kevinaangstadt/ARC86-512/hardware/ARC86-512.kicad_sch

## KiCad design hardware/ARC86-512.kicad_sch (2025-04-01, an earlier design)

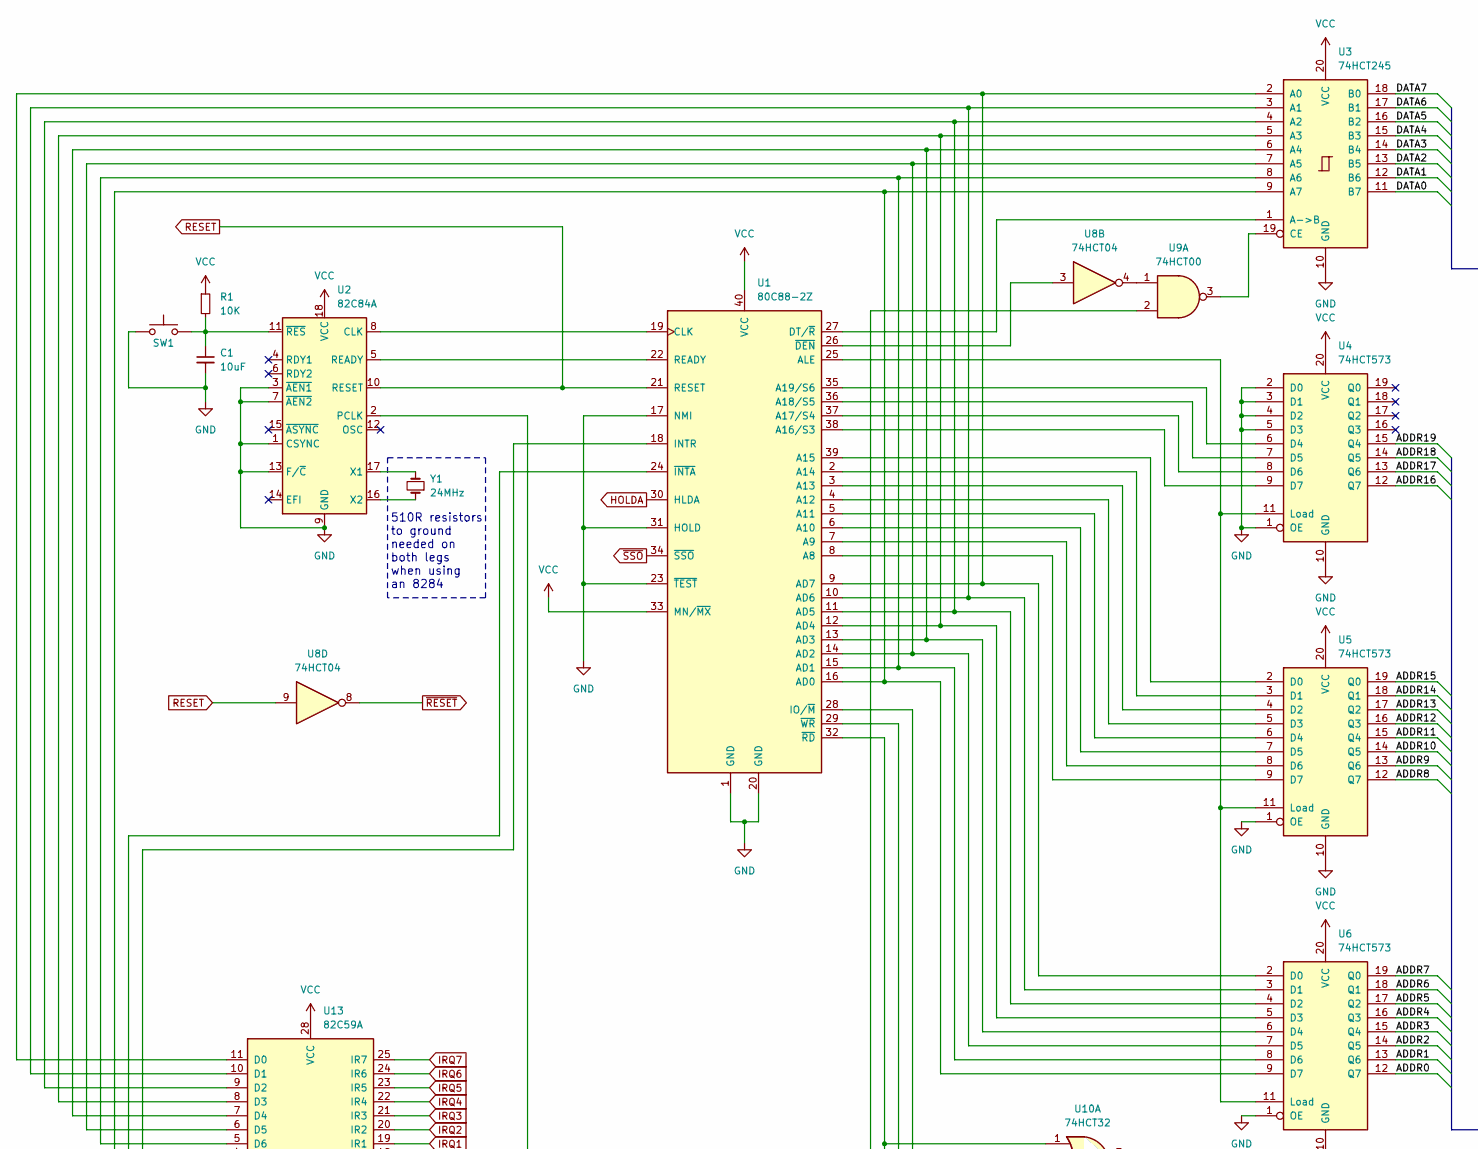
[picture p5: schematic ARC86-512.kicad_sch, part in row 1, column 1]

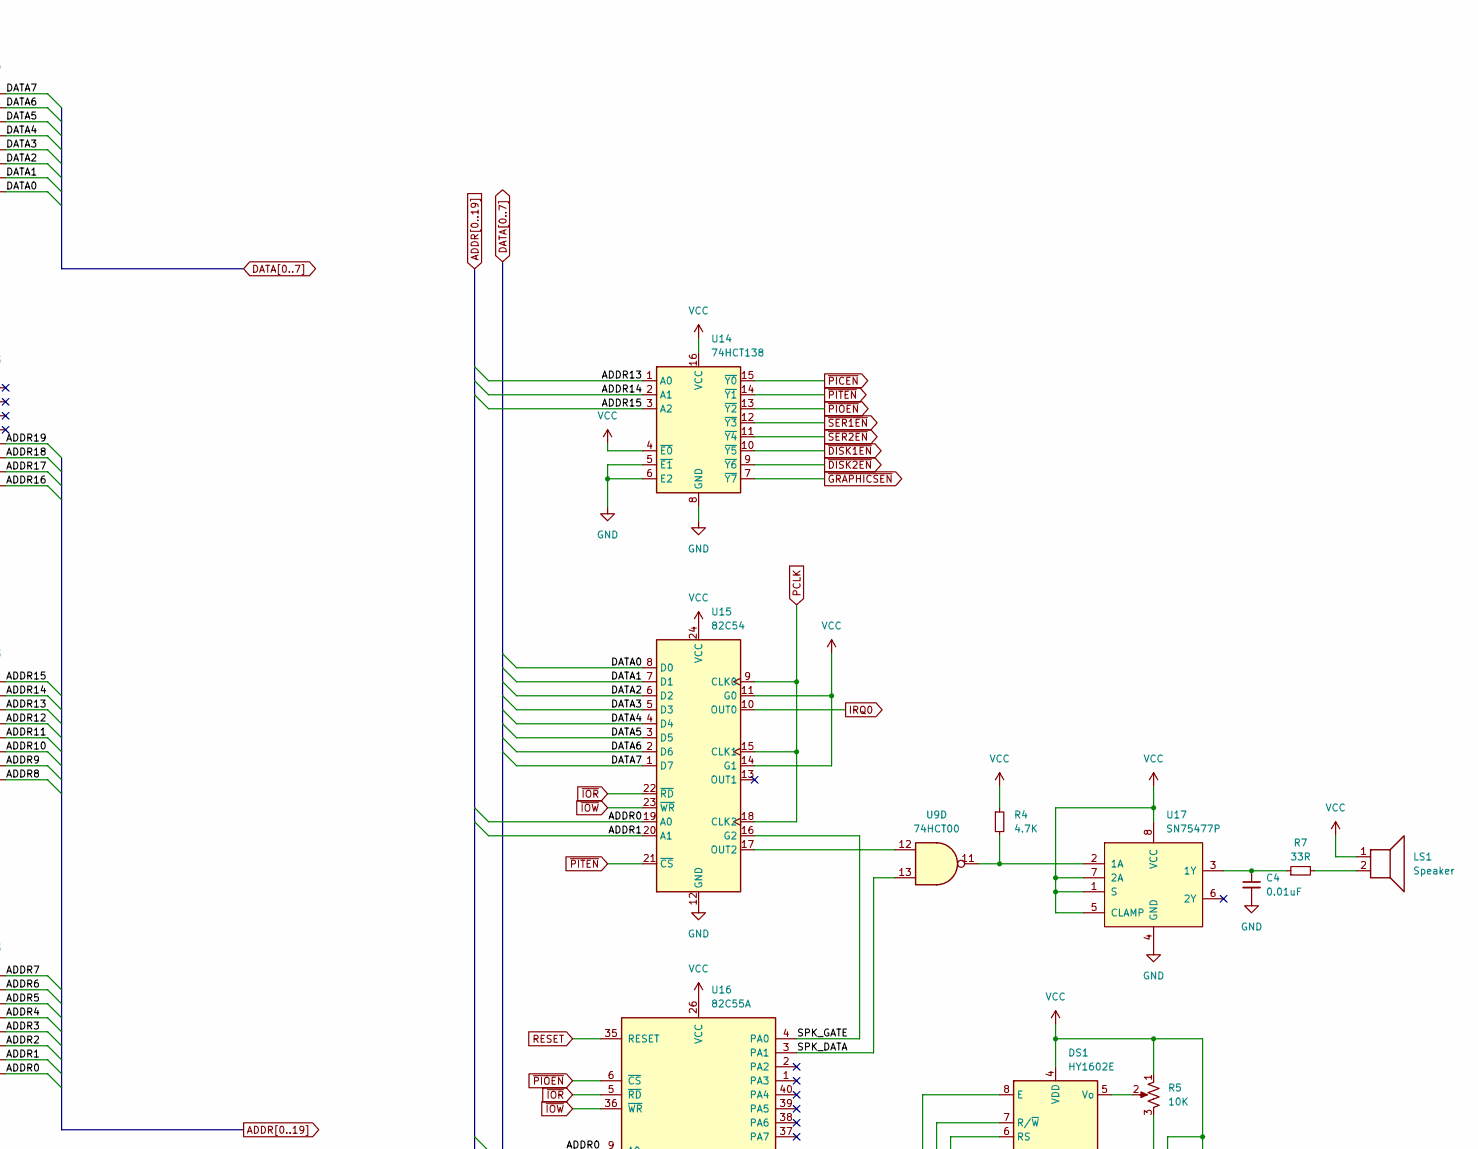
[picture p6: schematic ARC86-512.kicad_sch, part in row 1, column 2]

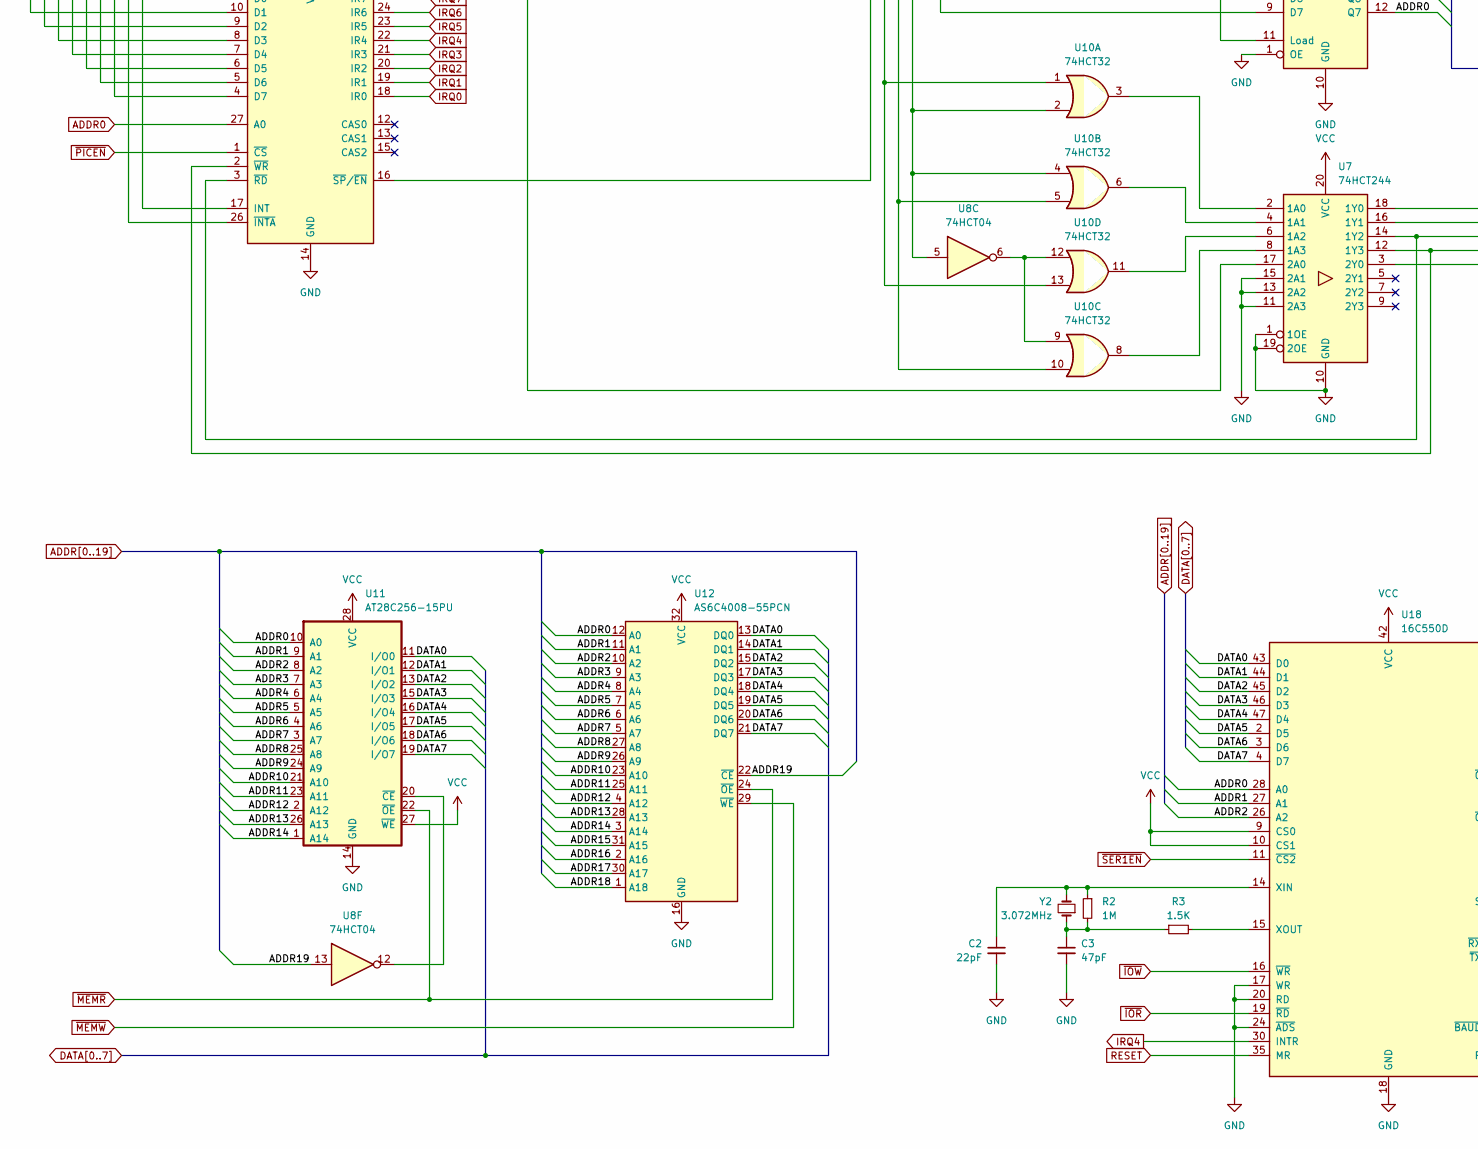
[picture p7: schematic ARC86-512.kicad_sch, part in row 2, column 1]

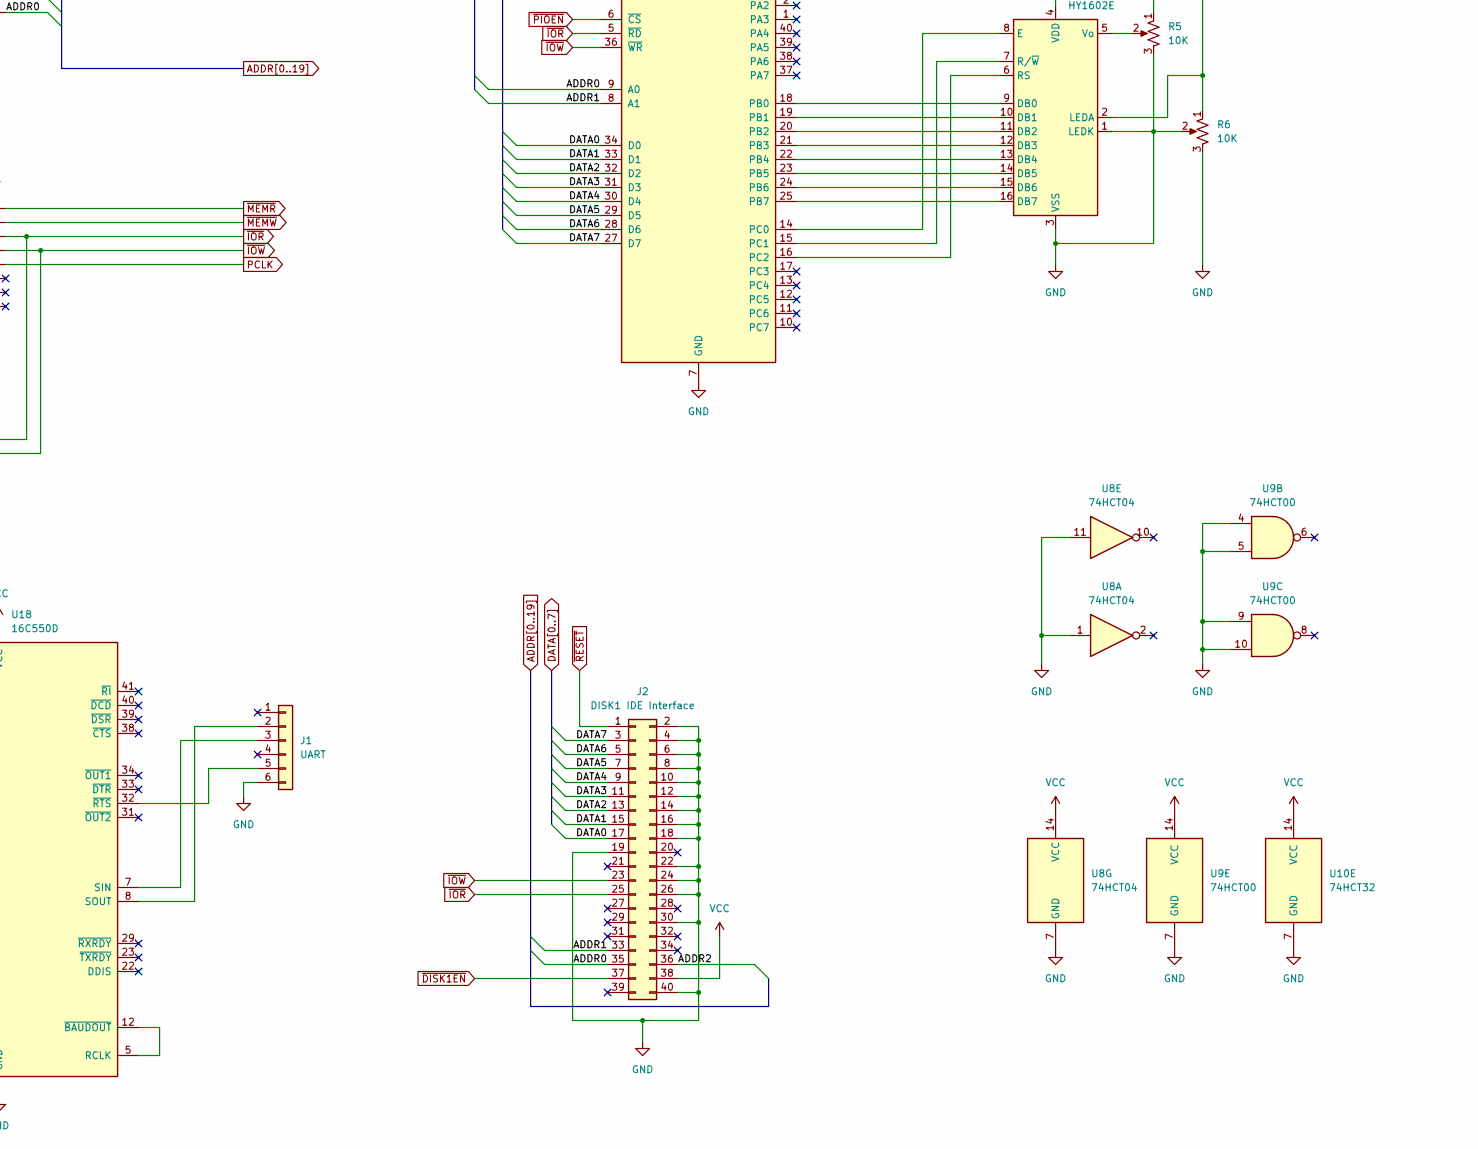
[picture p8: schematic ARC86-512.kicad_sch, part in row 2, column 2]

Parts:
C1: 10uF
C2: 22pF
C3: 47pF
C4: 0.01uF
DS1: HY1602E
J1: UART
J2: DISK1 IDE Interface
LS1: Speaker
R1, R5, R6: 10K
R2: 1M
R3: 1.5K
R4: 4.7K
R7: 33R
SW1: (no value)
U1: 80C88-2Z; DIP-40_W15.24mm_LongPads
U2: 82C84A; DIP-18_W7.62mm_LongPads
U3: 74HCT245; DIP-20_W7.62mm_LongPads
U4, U5, U6: 74HCT573; DIP-20_W7.62mm_LongPads
U7: 74HCT244
U8: 74HCT04
U9: 74HCT00
U10: 74HCT32
U11: AT28C256-15PU; DIP-28_W15.24mm_LongPads; PARTREV B
U12: AS6C4008-55PCN; DIP-32_W15.24mm
U13: 82C59A; DIP-28_W15.24mm
U14: 74HCT138
U15: 82C54; DIP-24_W15.24mm
U16: 82C55A; DIP-40_W15.24mm
U17: SN75477P; DIP-8_W7.62mm_LongPads
U18: 16C550D; DIP-48_W15.24mm_LongPads
Y1: 24MHz
Y2: 3.072MHz

Connections:
ADDR0: J2.35, U6.12 (Q7), U11.10 (A0), U12.12 (A0), U13.27 (A0), U15.19 (A0), U16.9 (A0), U18.28 (A0)
ADDR1: J2.33, U6.13 (Q6), U11.9 (A1), U12.11 (A1), U15.20 (A1), U16.8 (A1), U18.27 (A1)
ADDR2: J2.36, U6.14 (Q5), U11.8 (A2), U12.10 (A2), U18.26 (A2)
ADDR3: U6.15 (Q4), U11.7 (A3), U12.9 (A3)
ADDR4: U6.16 (Q3), U11.6 (A4), U12.8 (A4)
ADDR5: U6.17 (Q2), U11.5 (A5), U12.7 (A5)
ADDR6: U6.18 (Q1), U11.4 (A6), U12.6 (A6)
ADDR7: U6.19 (Q0), U11.3 (A7), U12.5 (A7)
ADDR8: U5.12 (Q7), U11.25 (A8), U12.27 (A8)
ADDR9: U5.13 (Q6), U11.24 (A9), U12.26 (A9)
ADDR10: U5.14 (Q5), U11.21 (A10), U12.23 (A10)
ADDR11: U5.15 (Q4), U11.23 (A11), U12.25 (A11)
ADDR12: U5.16 (Q3), U11.2 (A12), U12.4 (A12)
ADDR13: U5.17 (Q2), U11.26 (A13), U12.28 (A13), U14.1 (A0)
ADDR14: U5.18 (Q1), U11.1 (A14), U12.3 (A14), U14.2 (A1)
ADDR15: U5.19 (Q0), U12.31 (A15), U14.3 (A2)
ADDR16: U4.12 (Q7), U12.2 (A16)
ADDR17: U4.13 (Q6), U12.30 (A17)
ADDR18: U4.14 (Q5), U12.1 (A18)
ADDR19: U4.15 (Q4), U8.13, U12.22 (~CE)
DATA0: J2.17, U3.11 (B7), U11.11 (I/O0), U12.13 (DQ0), U15.8 (D0), U16.34 (D0), U18.43 (D0)
DATA1: J2.15, U3.12 (B6), U11.12 (I/O1), U12.14 (DQ1), U15.7 (D1), U16.33 (D1), U18.44 (D1)
DATA2: J2.13, U3.13 (B5), U11.13 (I/O2), U12.15 (DQ2), U15.6 (D2), U16.32 (D2), U18.45 (D2)
DATA3: J2.11, U3.14 (B4), U11.15 (I/O3), U12.17 (DQ3), U15.5 (D3), U16.31 (D3), U18.46 (D3)
DATA4: J2.9, U3.15 (B3), U11.16 (I/O4), U12.18 (DQ4), U15.4 (D4), U16.30 (D4), U18.47 (D4)
DATA5: J2.7, U3.16 (B2), U11.17 (I/O5), U12.19 (DQ5), U15.3 (D5), U16.29 (D5), U18.2 (D5)
DATA6: J2.5, U3.17 (B1), U11.18 (I/O6), U12.20 (DQ6), U15.2 (D6), U16.28 (D6), U18.3 (D6)
DATA7: J2.3, U3.18 (B0), U11.19 (I/O7), U12.21 (DQ7), U15.1 (D7), U16.27 (D7), U18.4 (D7)
GND: C1.2, C2.2, C3.2, C4.2, DS1.1 (LEDK), DS1.3 (VSS), J1.6, J2.2, J2.4, J2.6, J2.8, J2.10, J2.12, J2.14, J2.16, J2.18, J2.19, J2.22, J2.24, J2.26, J2.30, J2.40, R5.3, R6.2, R6.3, SW1.1, U1.1 (GND), U1.17 (NMI), U1.20 (GND), U1.23 (~TEST), U1.31 (HOLD), U2.1 (CSYNC), U2.3 (~AEN1), U2.7 (~AEN2), U2.9 (GND), U2.13 (F/~C), U3.10 (GND), U4.1 (OE), U4.2 (D0), U4.3 (D1), U4.4 (D2), U4.5 (D3), U4.10 (GND), U5.1 (OE), U5.10 (GND), U6.1 (OE), U6.10 (GND), U7.1 (1OE), U7.10 (GND), U7.11 (2A3), U7.13 (2A2), U7.15 (2A1), U7.19 (2OE), U8.1, U8.7 (GND), U8.11, U9.4, U9.5, U9.7 (GND), U9.9, U9.10, U10.7 (GND), U11.14 (GND), U12.16 (GND), U13.14 (GND), U14.5 (~E1), U14.6 (E2), U14.8 (GND), U15.12 (GND), U16.7 (GND), U17.4 (GND), U18.17 (WR), U18.18 (GND), U18.20 (RD), U18.24 (~ADS)
HOLDA: U1.30 (HLDA)
IRQ0: U13.18 (IR0), U15.10 (OUT0)
IRQ1: U13.19 (IR1)
IRQ2: U13.20 (IR2)
IRQ3: U13.21 (IR3)
IRQ4: U13.22 (IR4), U18.30 (INTR)
IRQ5: U13.23 (IR5)
IRQ6: U13.24 (IR6)
IRQ7: U13.25 (IR7)
unnamed: C1.1, R1.2, SW1.2, U2.11 (~RES)
unnamed: C2.1, R2.1, U18.14 (XIN), Y2.2
unnamed: C3.1, R2.2, R3.1, Y2.1
unnamed: C4.1, R7.1, U17.3 (1Y)
unnamed: DS1.5 (Vo), R5.2
unnamed: DS1.6 (RS), U16.16 (PC2)
unnamed: DS1.7 (R/~W), U16.15 (PC1)
unnamed: DS1.8 (E), U16.14 (PC0)
unnamed: DS1.9 (DB0), U16.18 (PB0)
unnamed: DS1.10 (DB1), U16.19 (PB1)
unnamed: DS1.11 (DB2), U16.20 (PB2)
unnamed: DS1.12 (DB3), U16.21 (PB3)
unnamed: DS1.13 (DB4), U16.22 (PB4)
unnamed: DS1.14 (DB5), U16.23 (PB5)
unnamed: DS1.15 (DB6), U16.24 (PB6)
unnamed: DS1.16 (DB7), U16.25 (PB7)
unnamed: J1.2, U18.8 (SOUT)
unnamed: J1.3, U18.7 (SIN)
unnamed: J1.5, U18.32 (~RTS)
unnamed: LS1.2, R7.2
unnamed: R3.2, U18.15 (XOUT)
unnamed: R4.2, U9.11, U17.2 (1A)
unnamed: U1.2 (A14), U5.3 (D1)
unnamed: U1.3 (A13), U5.4 (D2)
unnamed: U1.4 (A12), U5.5 (D3)
unnamed: U1.5 (A11), U5.6 (D4)
unnamed: U1.6 (A10), U5.7 (D5)
unnamed: U1.7 (A9), U5.8 (D6)
unnamed: U1.8 (A8), U5.9 (D7)
unnamed: U1.9 (AD7), U3.2 (A0), U6.2 (D0), U13.11 (D0)
unnamed: U1.10 (AD6), U3.3 (A1), U6.3 (D1), U13.10 (D1)
unnamed: U1.11 (AD5), U3.4 (A2), U6.4 (D2), U13.9 (D2)
unnamed: U1.12 (AD4), U3.5 (A3), U6.5 (D3), U13.8 (D3)
unnamed: U1.13 (AD3), U3.6 (A4), U6.6 (D4), U13.7 (D4)
unnamed: U1.14 (AD2), U3.7 (A5), U6.7 (D5), U13.6 (D5)
unnamed: U1.15 (AD1), U3.8 (A6), U6.8 (D6), U13.5 (D6)
unnamed: U1.16 (AD0), U3.9 (A7), U6.9 (D7), U13.4 (D7)
unnamed: U1.18 (INTR), U13.17 (INT)
unnamed: U1.19 (CLK), U2.8 (CLK)
unnamed: U1.22 (READY), U2.5 (READY)
unnamed: U1.24 (~INTA), U13.26 (~INTA)
unnamed: U1.25 (ALE), U4.11 (Load), U5.11 (Load), U6.11 (Load)
unnamed: U1.26 (~DEN), U8.3
unnamed: U1.27 (DT/~R), U3.1 (A->B)
unnamed: U1.28 (IO/~M), U8.5, U10.2, U10.4
unnamed: U1.29 (~WR), U10.5, U10.10
unnamed: U1.32 (~RD), U10.1, U10.13
unnamed: U1.35 (A19/S6), U4.6 (D4)
unnamed: U1.36 (A18/S5), U4.7 (D5)
unnamed: U1.37 (A17/S4), U4.8 (D6)
unnamed: U1.38 (A16/S3), U4.9 (D7)
unnamed: U1.39 (A15), U5.2 (D0)
unnamed: U2.2 (PCLK), U7.17 (2A0)
unnamed: U2.16 (X2), Y1.1
unnamed: U2.17 (X1), Y1.2
unnamed: U3.19 (CE), U9.3
unnamed: U8.4, U9.1
unnamed: U7.2 (1A0), U10.3
unnamed: U7.4 (1A1), U10.6
unnamed: U7.8 (1A3), U10.8
unnamed: U7.6 (1A2), U10.11
unnamed: U8.6, U10.9, U10.12
unnamed: U8.12, U11.20 (~CE)
unnamed: U9.2, U13.16 (~SP/~EN)
unnamed: U9.12, U15.17 (OUT2)
unnamed: U18.5 (RCLK), U18.12 (~BAUDOUT)
PCLK: U7.3 (2Y0), U15.9 (CLK0), U15.15 (CLK1), U15.18 (CLK2)
RESET: U1.21 (RESET), U2.10 (RESET), U8.9, U16.35 (RESET), U18.35 (MR)
SPK_DATA: U9.13, U16.3 (PA1)
SPK_GATE: U15.16 (G2), U16.4 (PA0)
VCC: DS1.2 (LEDA), DS1.4 (VDD), J2.38, LS1.1, R1.1, R4.1, R5.1, R6.1, U1.33 (MN/~MX), U1.40 (VCC), U2.18 (VCC), U3.20 (VCC), U4.20 (VCC), U5.20 (VCC), U6.20 (VCC), U7.20 (VCC), U8.14 (VCC), U9.14 (VCC), U10.14 (VCC), U11.27 (~WE), U11.28 (VCC), U12.32 (VCC), U13.28 (VCC), U14.4 (~E0), U14.16 (VCC), U15.11 (G0), U15.14 (G1), U15.24 (VCC), U16.26 (VCC), U17.1 (S), U17.5 (CLAMP), U17.7 (2A), U17.8 (VCC), U18.9 (CS0), U18.10 (CS1), U18.42 (VCC)
~DISK1EN: J2.37, U14.10 (~Y5)
~DISK2EN: U14.9 (~Y6)
~GRAPHICSEN: U14.7 (~Y7)
~IOR: J2.25, U7.14 (1Y2), U13.3 (~RD), U15.22 (~RD), U16.5 (~RD), U18.19 (~RD)
~IOW: J2.23, U7.12 (1Y3), U13.2 (~WR), U15.23 (~WR), U16.36 (~WR), U18.16 (~WR)
~MEMR: U7.18 (1Y0), U11.22 (~OE), U12.24 (~OE)
~MEMW: U7.16 (1Y1), U12.29 (~WE)
~PICEN: U13.1 (~CS), U14.15 (~Y0)
~PIOEN: U14.13 (~Y2), U16.6 (~CS)
~PITEN: U14.14 (~Y1), U15.21 (~CS)
~RESET: J2.1, U8.8
~SER1EN: U14.12 (~Y3), U18.11 (~CS2)
~SER2EN: U14.11 (~Y4)
~SSO: U1.34 (~SSO)

Notes on the sheet:
510R resistors to ground needed on both legs when using an 8284
